ciwhitfill/buffer-pedal/simulation/Buffer Pedal.asc

C1: cap; 10µ
C2: cap; 10µ
C3: cap; 47µ
D1: diode; 1N4007
D2: LED; LedGreen
J1: njf; J113
J2: njf; J113
R1: res; 330
R3: res; 10Meg
R4: res; 10Meg
R6: res; 10Meg
R7: res; 4.7k
RL: res; 100k
V1: voltage; SINE(9 0 60); AC 0; Rser=1
VSource: voltage; SINE(0 1 1k); AC 1
Vtest: voltage; ""; AC 1
Named nets: 0, Out, In
.op
.ac oct 100 10 100k
.tran .25
.noise V(Out) VSource oct 100 10 100k
